TaminoDesign/keyboard/keyboard.kicad_sch

## KiCad design keyboard.kicad_sch (2026-07-28)

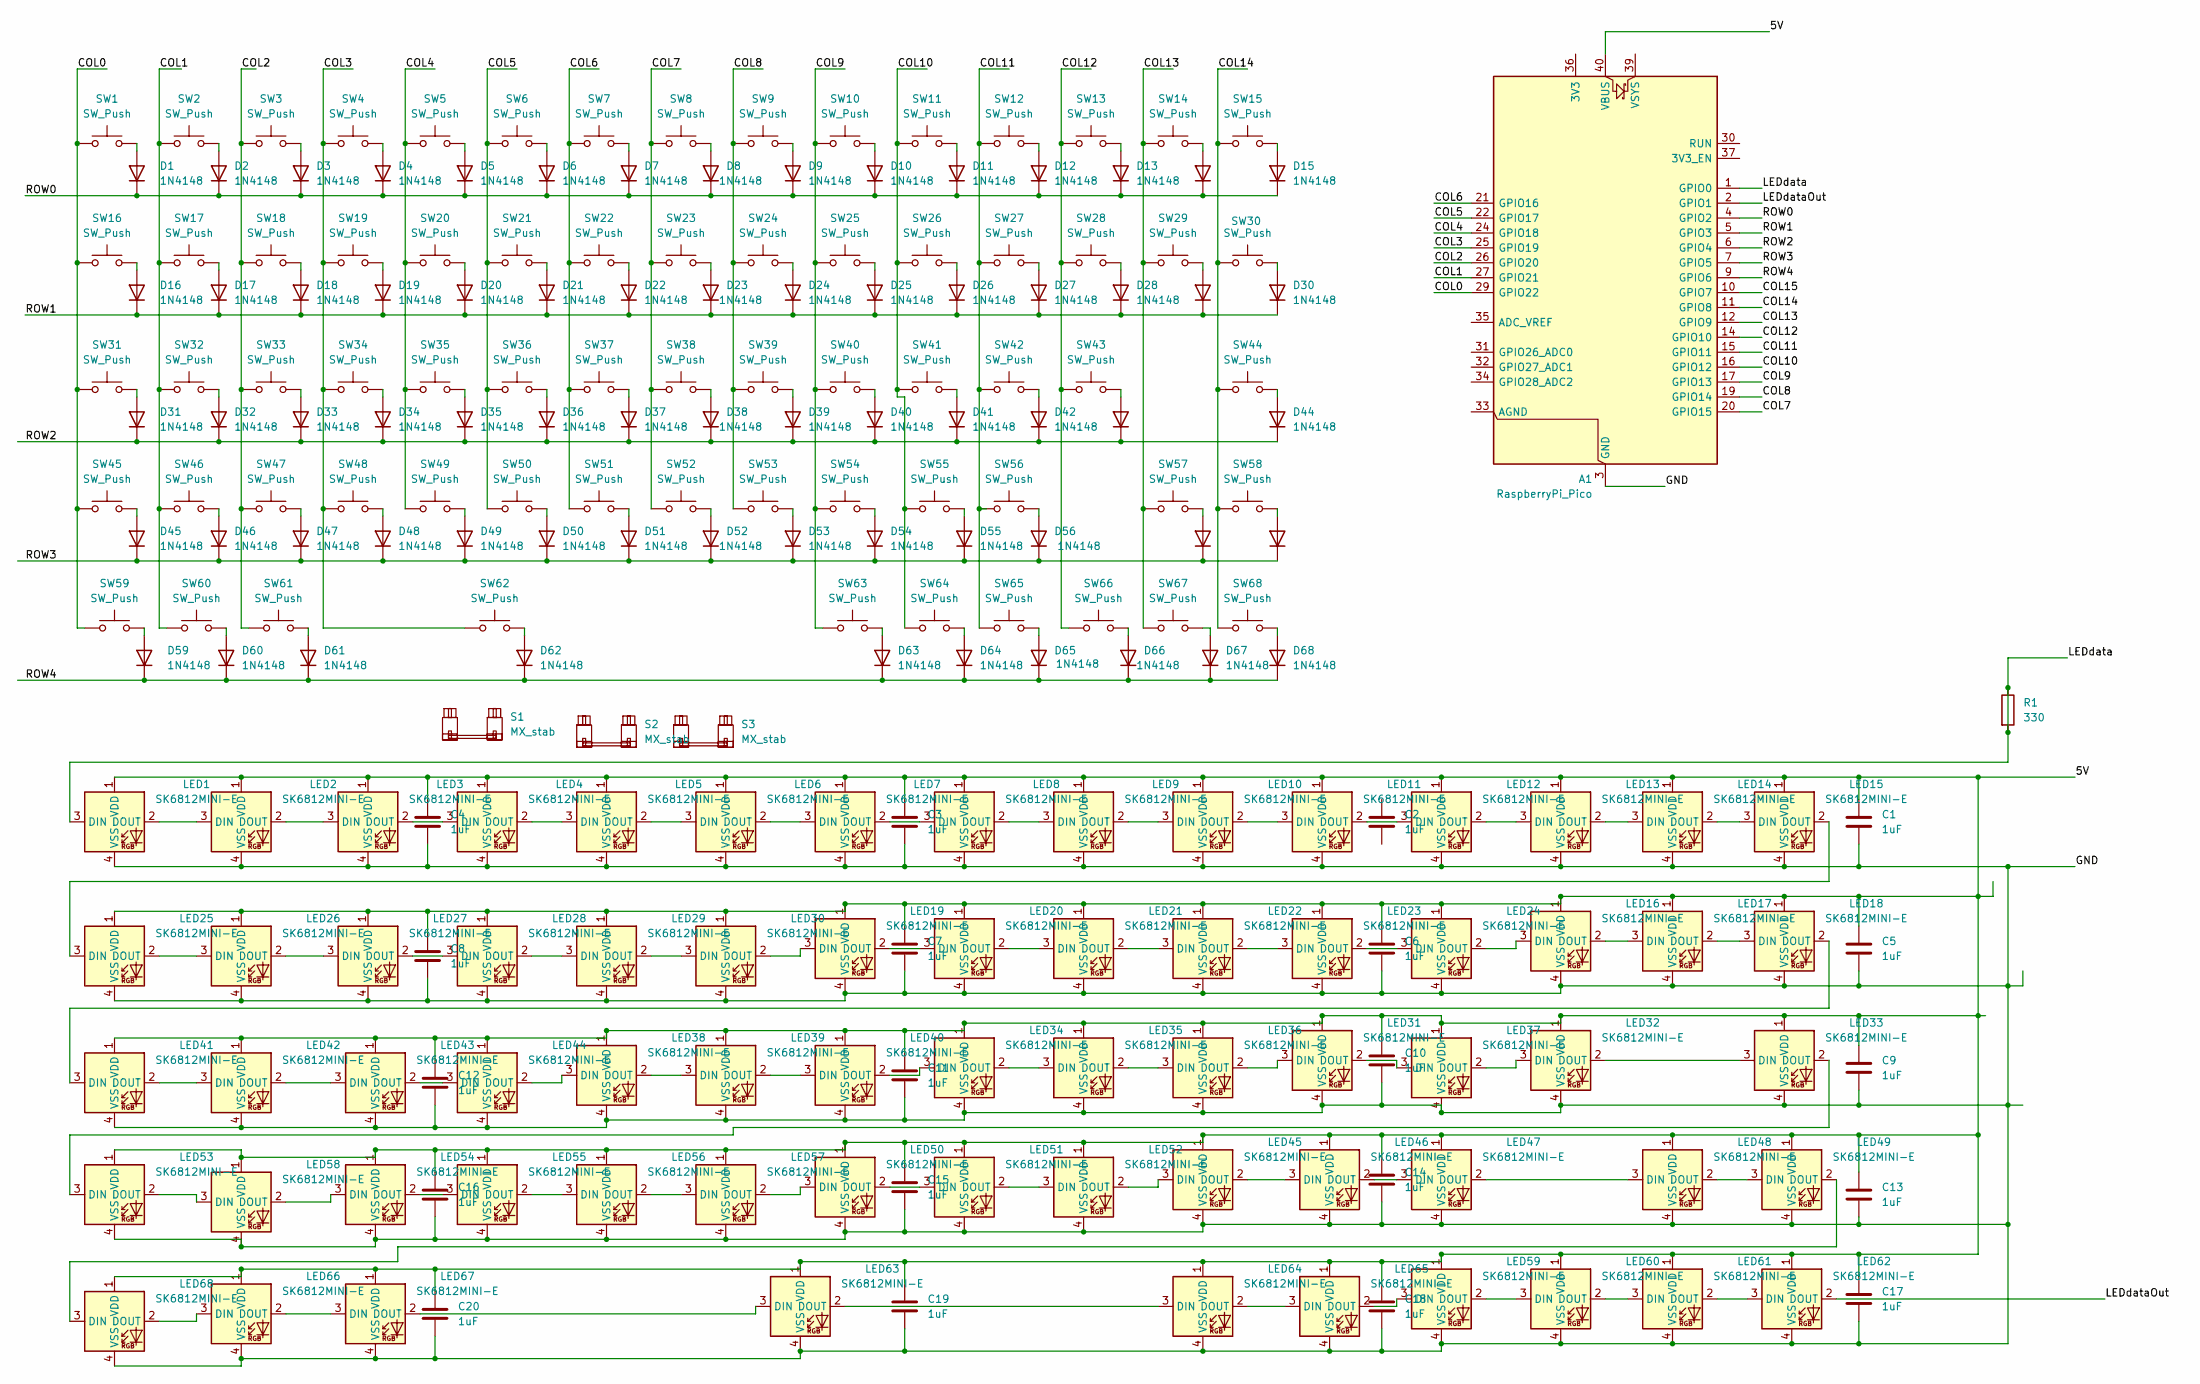
[picture p7: schematic keyboard.kicad_sch]

Parts:
A1: RaspberryPi_Pico; RaspberryPi_Pico_Common_THT
C1, C2, C3, C4, C5, C6, C7, C8, C9, C10, C11, C12, C13, C14, C15, C16, C17, C18, C19, C20: 1uF; C_0603_1608Metric
D1, D2, D3, D4, D5, D6, D7, D8, D9, D10, D11, D12, D13, D14, D15, D16, D17, D18, D19, D20, D21, D22, D23, D24, D25, D26, D27, D28, D29, D30, D31, D32, D33, D34, D35, D36, D37, D38, D39, D40, D41, D42, D43, D44, D45, D46, D47, D48, D49, D50, D51, D52, D53, D54, D55, D56, D57, D58, D59, D60, D61, D62, D63, D64, D65, D66, D67, D68: 1N4148; D_DO-35_SOD27_P7.62mm_Horizontal
LED1, LED2, LED3, LED4, LED5, LED6, LED7, LED8, LED9, LED10, LED11, LED12, LED13, LED14, LED15, LED16, LED17, LED18, LED19, LED20, LED21, LED22, LED23, LED24, LED25, LED26, LED27, LED28, LED29, LED30, LED31, LED32, LED33, LED34, LED35, LED36, LED37, LED38, LED39, LED40, LED41, LED42, LED43, LED44, LED45, LED46, LED47, LED48, LED49, LED50, LED51, LED52, LED53, LED54, LED55, LED56, LED57, LED58, LED59, LED60, LED61, LED62, LED63, LED64, LED65, LED66, LED67, LED68: SK6812MINI-E; LED_6028R
R1: 330; R_Axial_DIN0207_L6.3mm_D2.5mm_P10.16mm_Horizontal
S1, S2, S3: MX_stab; STAB_MX_P_6.25u
SW1, SW2, SW3, SW4, SW5, SW6, SW7, SW8, SW9, SW10, SW11, SW12, SW13, SW14, SW15, SW16, SW17, SW18, SW19, SW20, SW21, SW22, SW23, SW24, SW25, SW26, SW27, SW28, SW29, SW30, SW31, SW32, SW33, SW34, SW35, SW36, SW37, SW38, SW39, SW40, SW41, SW42, SW43, SW44, SW45, SW46, SW47, SW48, SW49, SW50, SW51, SW52, SW53, SW54, SW55, SW56, SW57, SW58, SW59, SW60, SW61, SW62, SW63, SW64, SW65, SW66, SW67, SW68: SW_Push; SW_MX_1u

Connections:
5V: A1.40 (VBUS), C1.1, C3.1, C4.1, C5.1, C6.1, C7.1, C8.1, C9.1, C10.1, C11.1, C12.1, C13.1, C14.1, C15.1, C16.1, C17.1, C18.1, C19.1, C20.1, LED1.1 (VDD), LED2.1 (VDD), LED3.1 (VDD), LED4.1 (VDD), LED5.1 (VDD), LED6.1 (VDD), LED7.1 (VDD), LED8.1 (VDD), LED9.1 (VDD), LED10.1 (VDD), LED11.1 (VDD), LED12.1 (VDD), LED13.1 (VDD), LED14.1 (VDD), LED15.1 (VDD), LED16.1 (VDD), LED17.1 (VDD), LED18.1 (VDD), LED19.1 (VDD), LED20.1 (VDD), LED21.1 (VDD), LED22.1 (VDD), LED23.1 (VDD), LED24.1 (VDD), LED25.1 (VDD), LED26.1 (VDD), LED27.1 (VDD), LED28.1 (VDD), LED29.1 (VDD), LED30.1 (VDD), LED31.1 (VDD), LED32.1 (VDD), LED33.1 (VDD), LED34.1 (VDD), LED35.1 (VDD), LED36.1 (VDD), LED37.1 (VDD), LED38.1 (VDD), LED39.1 (VDD), LED40.1 (VDD), LED41.1 (VDD), LED42.1 (VDD), LED43.1 (VDD), LED44.1 (VDD), LED45.1 (VDD), LED46.1 (VDD), LED47.1 (VDD), LED48.1 (VDD), LED49.1 (VDD), LED50.1 (VDD), LED51.1 (VDD), LED52.1 (VDD), LED53.1 (VDD), LED54.1 (VDD), LED55.1 (VDD), LED56.1 (VDD), LED57.1 (VDD), LED58.1 (VDD), LED59.1 (VDD), LED60.1 (VDD), LED61.1 (VDD), LED62.1 (VDD), LED63.1 (VDD), LED64.1 (VDD), LED65.1 (VDD), LED66.1 (VDD), LED67.1 (VDD), LED68.1 (VDD)
COL0: A1.29 (GPIO22), SW1.1, SW16.1, SW31.1, SW45.1, SW59.1
COL1: A1.27 (GPIO21), SW2.1, SW17.1, SW32.1, SW46.1, SW60.1
COL2: A1.26 (GPIO20), SW3.1, SW18.1, SW33.1, SW47.1, SW61.1
COL3: A1.25 (GPIO19), SW4.1, SW19.1, SW34.1, SW48.1, SW62.1
COL4: A1.24 (GPIO18), SW5.1, SW20.1, SW35.1, SW49.1
COL5: A1.22 (GPIO17), SW6.1, SW21.1, SW36.1, SW50.1
COL6: A1.21 (GPIO16), SW7.1, SW22.1, SW37.1, SW51.1
COL7: A1.20 (GPIO15), SW8.1, SW23.1, SW38.1, SW52.1
COL8: A1.19 (GPIO14), SW9.1, SW24.1, SW39.1, SW53.1
COL9: A1.17 (GPIO13), SW10.1, SW25.1, SW40.1, SW54.1, SW63.1
COL10: A1.16 (GPIO12), SW11.1, SW26.1, SW41.1, SW55.1, SW64.1
COL11: A1.15 (GPIO11), SW12.1, SW27.1, SW42.1, SW56.1, SW65.1
COL12: A1.14 (GPIO10), SW13.1, SW28.1, SW43.1, SW66.1
COL13: A1.12 (GPIO9), SW14.1, SW29.1, SW57.1, SW67.1
COL14: A1.11 (GPIO8), SW15.1, SW30.1, SW44.1, SW58.1, SW68.1
COL15: A1.10 (GPIO7)
GND: A1.3 (GND), A1.8 (GND), A1.13 (GND), A1.18 (GND), A1.23 (GND), A1.28 (GND), A1.38 (GND), C1.2, C3.2, C4.2, C5.2, C6.2, C7.2, C8.2, C9.2, C10.2, C11.2, C12.2, C13.2, C14.2, C15.2, C16.2, C17.2, C18.2, C19.2, C20.2, LED1.4 (VSS), LED2.4 (VSS), LED3.4 (VSS), LED4.4 (VSS), LED5.4 (VSS), LED6.4 (VSS), LED7.4 (VSS), LED8.4 (VSS), LED9.4 (VSS), LED10.4 (VSS), LED11.4 (VSS), LED12.4 (VSS), LED13.4 (VSS), LED14.4 (VSS), LED15.4 (VSS), LED16.4 (VSS), LED17.4 (VSS), LED18.4 (VSS), LED19.4 (VSS), LED20.4 (VSS), LED21.4 (VSS), LED22.4 (VSS), LED23.4 (VSS), LED24.4 (VSS), LED25.4 (VSS), LED26.4 (VSS), LED27.4 (VSS), LED28.4 (VSS), LED29.4 (VSS), LED30.4 (VSS), LED31.4 (VSS), LED32.4 (VSS), LED33.4 (VSS), LED34.4 (VSS), LED35.4 (VSS), LED36.4 (VSS), LED37.4 (VSS), LED38.4 (VSS), LED39.4 (VSS), LED40.4 (VSS), LED41.4 (VSS), LED42.4 (VSS), LED43.4 (VSS), LED44.4 (VSS), LED45.4 (VSS), LED46.4 (VSS), LED47.4 (VSS), LED48.4 (VSS), LED49.4 (VSS), LED50.4 (VSS), LED51.4 (VSS), LED52.4 (VSS), LED53.4 (VSS), LED54.4 (VSS), LED55.4 (VSS), LED56.4 (VSS), LED57.4 (VSS), LED58.4 (VSS), LED59.4 (VSS), LED60.4 (VSS), LED61.4 (VSS), LED62.4 (VSS), LED63.4 (VSS), LED64.4 (VSS), LED65.4 (VSS), LED66.4 (VSS), LED67.4 (VSS), LED68.4 (VSS)
LEDdata: A1.1 (GPIO0), LED1.3 (DIN), R1.1, R1.2
LEDdataOut: A1.2 (GPIO1), LED62.2 (DOUT)
unnamed: D1.2 (A), SW1.2
unnamed: D2.2 (A), SW2.2
unnamed: D3.2 (A), SW3.2
unnamed: D4.2 (A), SW4.2
unnamed: D5.2 (A), SW5.2
unnamed: D6.2 (A), SW6.2
unnamed: D7.2 (A), SW7.2
unnamed: D8.2 (A), SW8.2
unnamed: D9.2 (A), SW9.2
unnamed: D10.2 (A), SW10.2
unnamed: D11.2 (A), SW11.2
unnamed: D12.2 (A), SW12.2
unnamed: D13.2 (A), SW13.2
unnamed: D14.2 (A), SW14.2
unnamed: D15.2 (A), SW15.2
unnamed: D16.2 (A), SW16.2
unnamed: D17.2 (A), SW17.2
unnamed: D18.2 (A), SW18.2
unnamed: D19.2 (A), SW19.2
unnamed: D20.2 (A), SW20.2
unnamed: D21.2 (A), SW21.2
unnamed: D22.2 (A), SW22.2
unnamed: D23.2 (A), SW23.2
unnamed: D24.2 (A), SW24.2
unnamed: D25.2 (A), SW25.2
unnamed: D26.2 (A), SW26.2
unnamed: D27.2 (A), SW27.2
unnamed: D28.2 (A), SW28.2
unnamed: D29.2 (A), SW29.2
unnamed: D30.2 (A), SW30.2
unnamed: D31.2 (A), SW31.2
unnamed: D32.2 (A), SW32.2
unnamed: D33.2 (A), SW33.2
unnamed: D34.2 (A), SW34.2
unnamed: D35.2 (A), SW35.2
unnamed: D36.2 (A), SW36.2
unnamed: D37.2 (A), SW37.2
unnamed: D38.2 (A), SW38.2
unnamed: D39.2 (A), SW39.2
unnamed: D40.2 (A), SW40.2
unnamed: D41.2 (A), SW41.2
unnamed: D42.2 (A), SW42.2
unnamed: D43.2 (A), SW43.2
unnamed: D44.2 (A), SW44.2
unnamed: D45.2 (A), SW45.2
unnamed: D46.2 (A), SW46.2
unnamed: D47.2 (A), SW47.2
unnamed: D48.2 (A), SW48.2
unnamed: D49.2 (A), SW49.2
unnamed: D50.2 (A), SW50.2
unnamed: D51.2 (A), SW51.2
unnamed: D52.2 (A), SW52.2
unnamed: D53.2 (A), SW53.2
unnamed: D54.2 (A), SW54.2
unnamed: D55.2 (A), SW55.2
unnamed: D56.2 (A), SW56.2
unnamed: D57.2 (A), SW57.2
unnamed: D58.2 (A), SW58.2
unnamed: D59.2 (A), SW59.2
unnamed: D60.2 (A), SW60.2
unnamed: D61.2 (A), SW61.2
unnamed: D62.2 (A), SW62.2
unnamed: D63.2 (A), SW63.2
unnamed: D64.2 (A), SW64.2
unnamed: D65.2 (A), SW65.2
unnamed: D66.2 (A), SW66.2
unnamed: D67.2 (A), SW67.2
unnamed: D68.2 (A), SW68.2
unnamed: LED1.2 (DOUT), LED2.3 (DIN)
unnamed: LED2.2 (DOUT), LED3.3 (DIN)
unnamed: LED3.2 (DOUT), LED4.3 (DIN)
unnamed: LED4.2 (DOUT), LED5.3 (DIN)
unnamed: LED5.2 (DOUT), LED6.3 (DIN)
unnamed: LED6.2 (DOUT), LED7.3 (DIN)
unnamed: LED7.2 (DOUT), LED8.3 (DIN)
unnamed: LED8.2 (DOUT), LED9.3 (DIN)
unnamed: LED10.2 (DOUT), LED11.3 (DIN)
unnamed: LED9.2 (DOUT), LED10.3 (DIN)
unnamed: LED11.2 (DOUT), LED12.3 (DIN)
unnamed: LED12.2 (DOUT), LED13.3 (DIN)
unnamed: LED13.2 (DOUT), LED14.3 (DIN)
unnamed: LED14.2 (DOUT), LED15.3 (DIN)
unnamed: LED15.2 (DOUT), LED25.3 (DIN)
unnamed: LED16.2 (DOUT), LED17.3 (DIN)
unnamed: LED16.3 (DIN), LED24.2 (DOUT)
unnamed: LED17.2 (DOUT), LED18.3 (DIN)
unnamed: LED18.2 (DOUT), LED41.3 (DIN)
unnamed: LED19.2 (DOUT), LED20.3 (DIN)
unnamed: LED19.3 (DIN), LED30.2 (DOUT)
unnamed: LED20.2 (DOUT), LED21.3 (DIN)
unnamed: LED21.2 (DOUT), LED22.3 (DIN)
unnamed: LED22.2 (DOUT), LED23.3 (DIN)
unnamed: LED23.2 (DOUT), LED24.3 (DIN)
unnamed: LED25.2 (DOUT), LED26.3 (DIN)
unnamed: LED26.2 (DOUT), LED27.3 (DIN)
unnamed: LED27.2 (DOUT), LED28.3 (DIN)
unnamed: LED28.2 (DOUT), LED29.3 (DIN)
unnamed: LED29.2 (DOUT), LED30.3 (DIN)
unnamed: LED31.2 (DOUT), LED37.3 (DIN)
unnamed: LED31.3 (DIN), LED36.2 (DOUT)
unnamed: LED32.2 (DOUT), LED33.3 (DIN)
unnamed: LED32.3 (DIN), LED37.2 (DOUT)
unnamed: LED33.2 (DOUT), LED53.3 (DIN)
unnamed: LED34.2 (DOUT), LED35.3 (DIN)
unnamed: LED34.3 (DIN), LED40.2 (DOUT)
unnamed: LED35.2 (DOUT), LED36.3 (DIN)
unnamed: LED38.2 (DOUT), LED39.3 (DIN)
unnamed: LED38.3 (DIN), LED44.2 (DOUT)
unnamed: LED39.2 (DOUT), LED40.3 (DIN)
unnamed: LED41.2 (DOUT), LED42.3 (DIN)
unnamed: LED42.2 (DOUT), LED43.3 (DIN)
unnamed: LED43.2 (DOUT), LED44.3 (DIN)
unnamed: LED45.2 (DOUT), LED46.3 (DIN)
unnamed: LED45.3 (DIN), LED52.2 (DOUT)
unnamed: LED46.2 (DOUT), LED47.3 (DIN)
unnamed: LED47.2 (DOUT), LED48.3 (DIN)
unnamed: LED48.2 (DOUT), LED49.3 (DIN)
unnamed: LED49.2 (DOUT), LED68.3 (DIN)
unnamed: LED50.2 (DOUT), LED51.3 (DIN)
unnamed: LED50.3 (DIN), LED57.2 (DOUT)
unnamed: LED51.2 (DOUT), LED52.3 (DIN)
unnamed: LED53.2 (DOUT), LED58.3 (DIN)
unnamed: LED54.2 (DOUT), LED55.3 (DIN)
unnamed: LED54.3 (DIN), LED58.2 (DOUT)
unnamed: LED55.2 (DOUT), LED56.3 (DIN)
unnamed: LED56.2 (DOUT), LED57.3 (DIN)
unnamed: LED59.2 (DOUT), LED60.3 (DIN)
unnamed: LED59.3 (DIN), LED65.2 (DOUT)
unnamed: LED60.2 (DOUT), LED61.3 (DIN)
unnamed: LED61.2 (DOUT), LED62.3 (DIN)
unnamed: LED63.2 (DOUT), LED64.3 (DIN)
unnamed: LED63.3 (DIN), LED67.2 (DOUT)
unnamed: LED64.2 (DOUT), LED65.3 (DIN)
unnamed: LED66.2 (DOUT), LED67.3 (DIN)
unnamed: LED66.3 (DIN), LED68.2 (DOUT)
ROW0: A1.4 (GPIO2), D1.1 (K), D2.1 (K), D3.1 (K), D4.1 (K), D5.1 (K), D6.1 (K), D7.1 (K), D8.1 (K), D9.1 (K), D10.1 (K), D11.1 (K), D12.1 (K), D13.1 (K), D14.1 (K), D15.1 (K)
ROW1: A1.5 (GPIO3), D16.1 (K), D17.1 (K), D18.1 (K), D19.1 (K), D20.1 (K), D21.1 (K), D22.1 (K), D23.1 (K), D24.1 (K), D25.1 (K), D26.1 (K), D27.1 (K), D28.1 (K), D29.1 (K), D30.1 (K)
ROW2: A1.6 (GPIO4), D31.1 (K), D32.1 (K), D33.1 (K), D34.1 (K), D35.1 (K), D36.1 (K), D37.1 (K), D38.1 (K), D39.1 (K), D40.1 (K), D41.1 (K), D42.1 (K), D43.1 (K), D44.1 (K)
ROW3: A1.7 (GPIO5), D45.1 (K), D46.1 (K), D47.1 (K), D48.1 (K), D49.1 (K), D50.1 (K), D51.1 (K), D52.1 (K), D53.1 (K), D54.1 (K), D55.1 (K), D56.1 (K), D57.1 (K), D58.1 (K)
ROW4: A1.9 (GPIO6), D59.1 (K), D60.1 (K), D61.1 (K), D62.1 (K), D63.1 (K), D64.1 (K), D65.1 (K), D66.1 (K), D67.1 (K), D68.1 (K)
